xlysio/AeroDrive2D-Sensory-Data-Visualizer/hardware/aerodrive2d/aerodrive2d.kicad_sch

## KiCad design hardware/aerodrive2d/aerodrive2d.kicad_sch (2026-03-25)

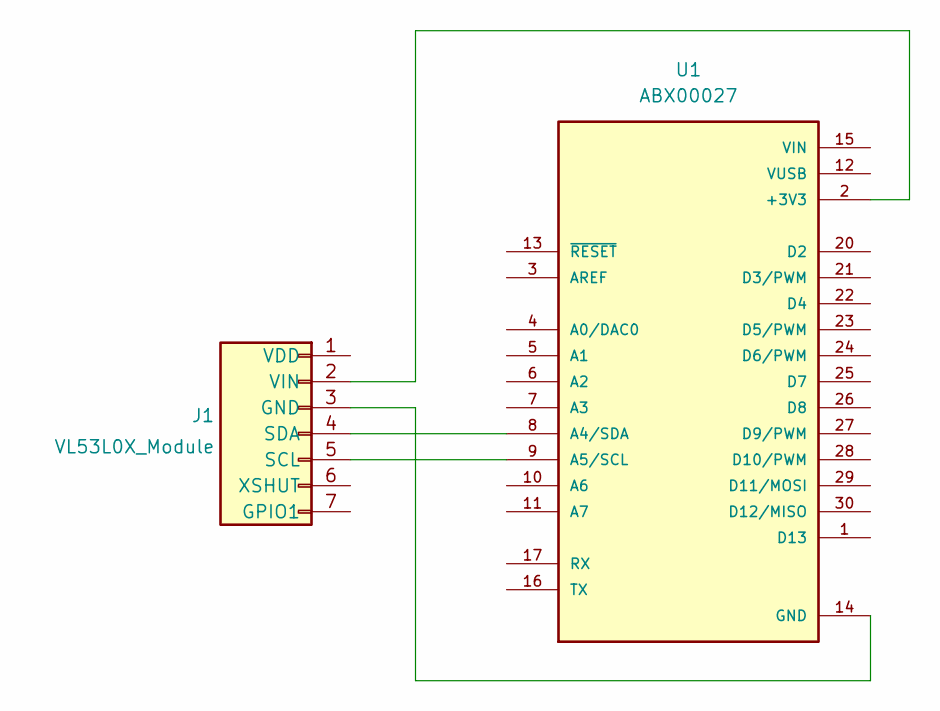
[picture p6: schematic aerodrive2d.kicad_sch]

Parts:
J1: VL53L0X_Module
U1: ABX00027; MODULE_ABX00027

Connections:
unnamed: J1.2 (VIN), U1.2 (+3V3)
unnamed: J1.3 (GND), U1.14 (GND), U1.19 (GND)
unnamed: J1.4 (SDA), U1.8 (A4/SDA)
unnamed: J1.5 (SCL), U1.9 (A5/SCL)
unnamed: U1.13 (~RESET), U1.18 (~RESET)
