xlysio/AeroDrive2D-Sensory-Data-Visualizer/software/pc_application/serialhandler.cpp

/**
 * @file serialhandler.cpp
 * @brief Implementation of the SerialHandler class.
 */
#include "serialhandler.h"

SerialHandler::SerialHandler(QObject *parent): QObject(parent)
{
    serial = new QSerialPort(this);

    // port configuration matching the microcontroller settings
    serial->setBaudRate(QSerialPort::Baud115200);
    serial->setDataBits(QSerialPort::Data8);
    serial->setParity(QSerialPort::NoParity);
    serial->setStopBits(QSerialPort::OneStop);
    serial->setFlowControl(QSerialPort::NoFlowControl);

    connect(serial, &QSerialPort::readyRead, this, &SerialHandler::onDataReady);
}

SerialHandler::~SerialHandler()
{

}

bool SerialHandler::openPort(const QString &portName)
{
    serial->setPortName(portName);

    if (!serial->open(QIODevice::ReadOnly))
    {
        return false;
    }

    return true;
}

bool SerialHandler::closePort()
{
    if (serial->isOpen())
    {
        serial->close();
        return true;
    }

    return false;
}

void SerialHandler::onDataReady()
{
    while (serial->canReadLine())
    {
        QString line = QString::fromUtf8(serial->readLine()).trimmed();

        // check frame prefix
        if (!line.startsWith("$"))
        {
            continue;
        }

        // find checksum separator
        int starIndex = line.lastIndexOf("*");
        if (starIndex == -1)
        {
            continue;
        }

        // extract payload and checksum from serial data
        QString payload = line.mid(1, starIndex - 1);
        QString checksumStr = line.mid(starIndex + 1);

        int computed = 0;
        for (int i = 0; i < payload.size(); ++i)
        {
            computed ^= payload.at(i).toLatin1();
        }

        // compare computed checksum with received checksum
        bool checksumOk;
        int received = checksumStr.toInt(&checksumOk, 16);
        if(!checksumOk || computed != received)
        {
            continue;
        }

        // check frame type prefix
        if (!payload.startsWith("AD,"))
        {
            continue;
        }

        // remove prefix and split into fields
        payload = payload.mid(3);
        QStringList data = payload.split(",");

        // validate amount of fields
        if (data.size() != 5)
        {
            continue;
        }

        // convert fields to floats
        bool ok0, ok1, ok2, ok3, ok4;
        float measuredDist = data[0].toFloat(&ok0);
        float realDist = data[1].toFloat(&ok1);
        float accDeg = data[2].toFloat(&ok2);
        float gyroDeg = data[3].toFloat(&ok3);
        float angleDeg = data[4].toFloat(&ok4);

        // emit signal only if all conversions succeeded
        if (ok0 && ok1 && ok2 && ok3 && ok4)
        {
            emit dataReceived(measuredDist, realDist, accDeg, gyroDeg, angleDeg);
        }
    }
}

QStringList SerialHandler::availablePorts()
{
    QStringList portNames;
    for (const QSerialPortInfo &info: QSerialPortInfo::availablePorts())
    {
        portNames.append(info.portName());
    }

    return portNames;
}
